SunDevilRocketry/Ground-Station-Telemetry/CAD/3Dfiles/T491A106K010AT.step

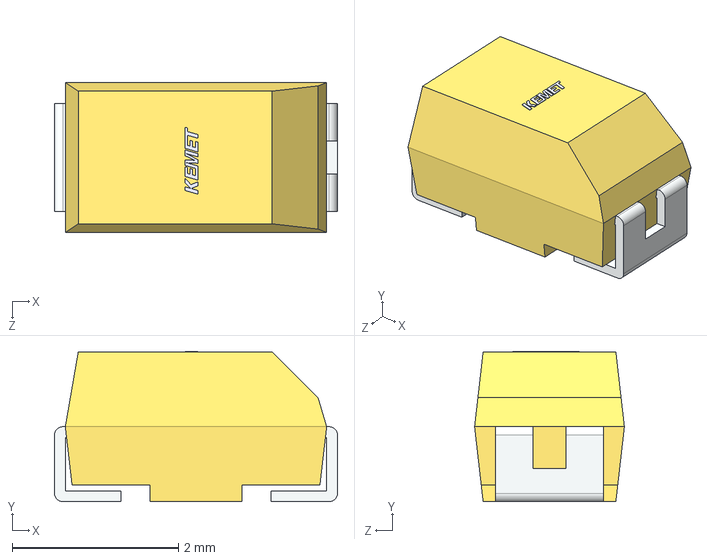
[picture p17: CAD file, 2022-10-11]
CAD/3Dfiles/T491A106K010AT.step
3.40 x 1.81 x 1.80 mm
