SunDevilRocketry/Ground-Station-Telemetry/CAD/3Dfiles/142-0701-801.STEP

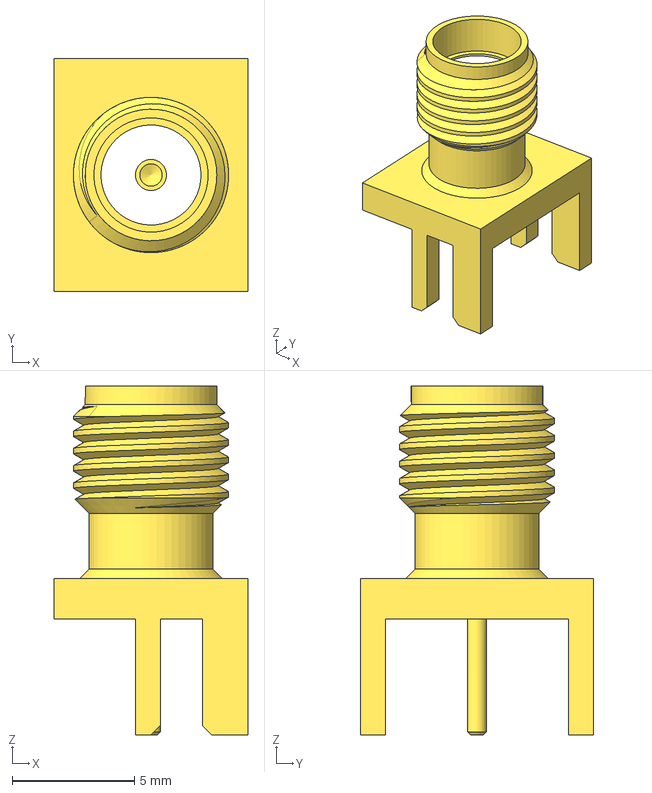
[picture p18: CAD file, 2022-10-11]
CAD/3Dfiles/142-0701-801.STEP
7.92 x 9.53 x 14.3 mm
