SunDevilRocketry/Ground-Station-Telemetry/CAD/3Dfiles/SS-52300-001--3DModel-STEP-56544.STEP

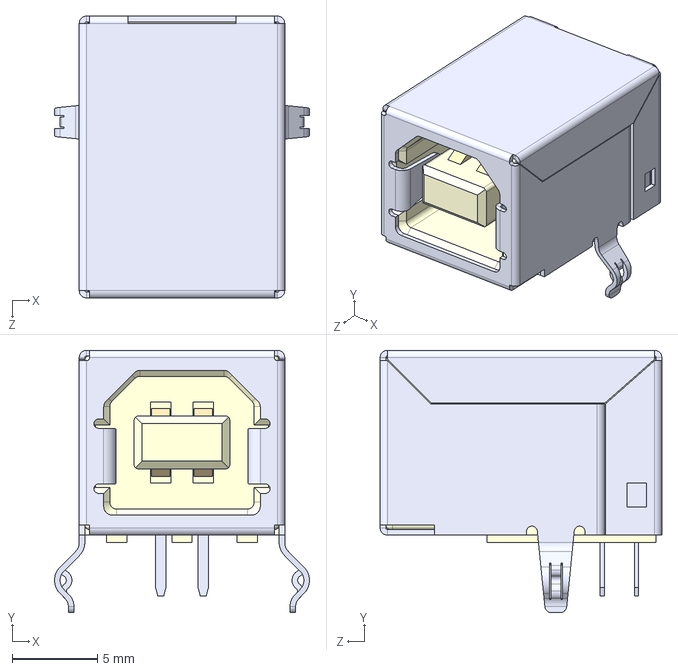
[picture p19: CAD file, 2022-10-11]
CAD/3Dfiles/SS-52300-001--3DModel-STEP-56544.STEP
14.9 x 15.4 x 16.5 mm
