SunDevilRocketry/Ground-Station-Telemetry/CAD/3Dfiles/282837-2.step

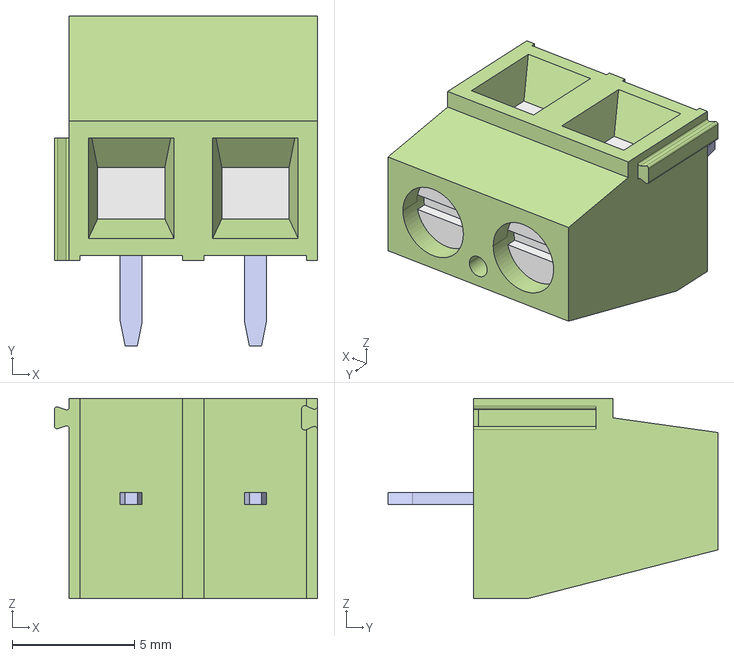
[picture p20: CAD file, 2023-04-09]
CAD/3Dfiles/282837-2.step
10.8 x 13.5 x 8.20 mm
